Rizz071/GearTest/Docs/2016_10_17_13_23_45.png

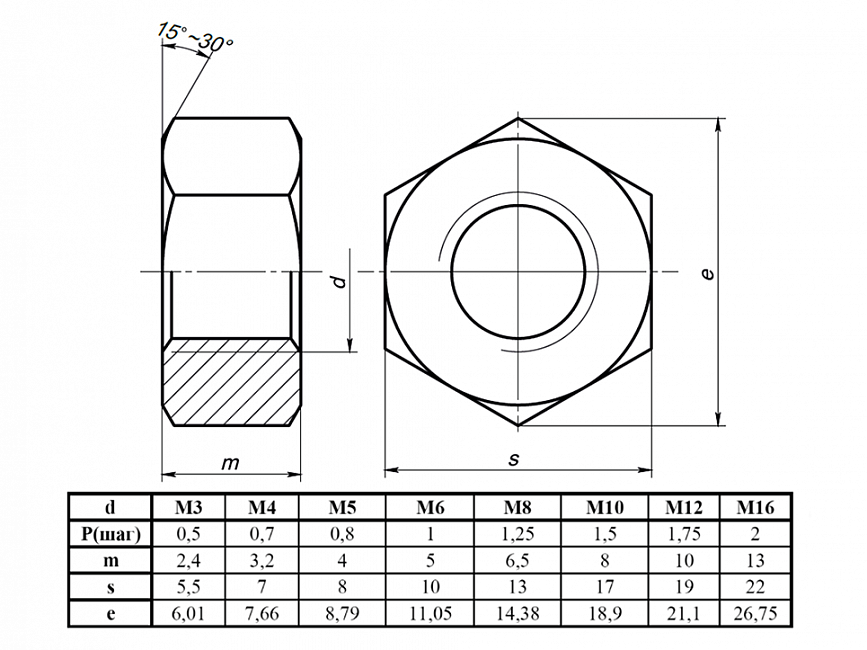
Docs/2016_10_17_13_23_45.png
