Rizz071/GearTest/Docs/6924317209.webp

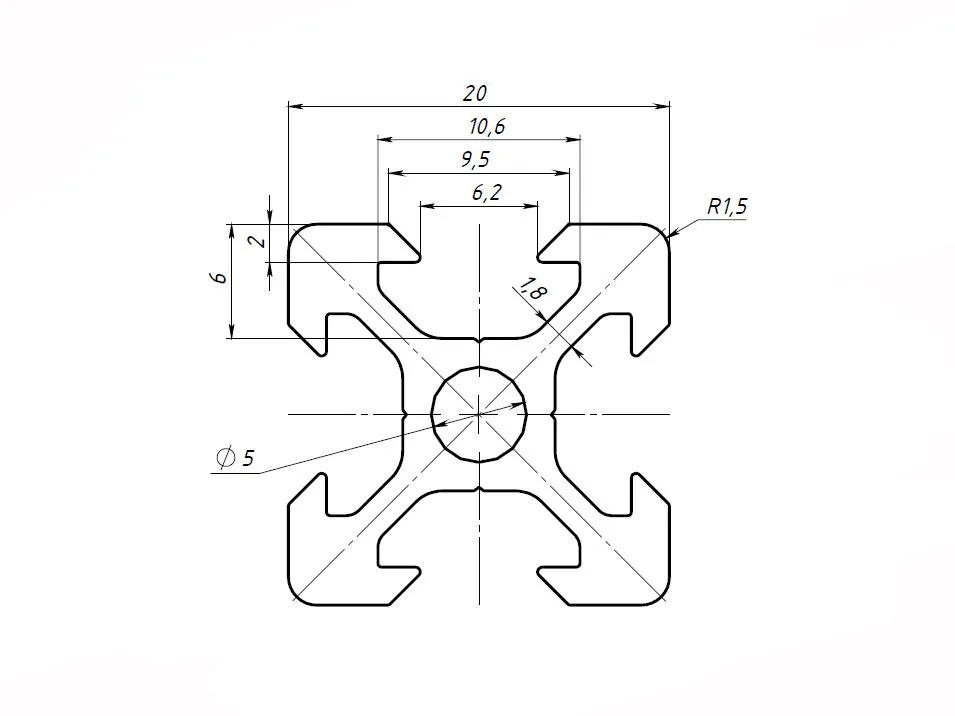
Docs/6924317209.webp
