Rizz071/GearTest/Docs/A263_CHertezh.jpg

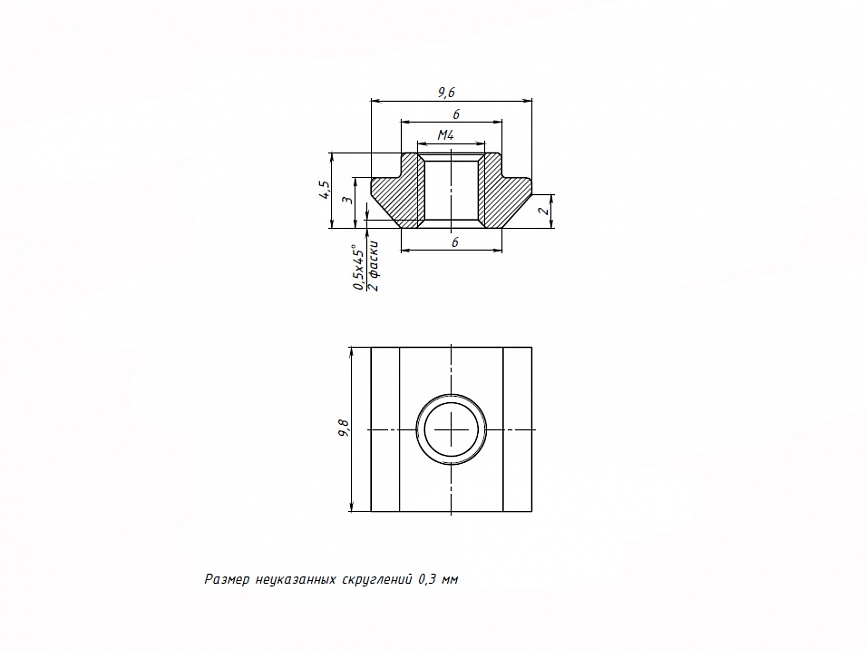
Docs/A263_CHertezh.jpg
