Rizz071/GearTest/Docs/D1925 Shaft Copuling.webp

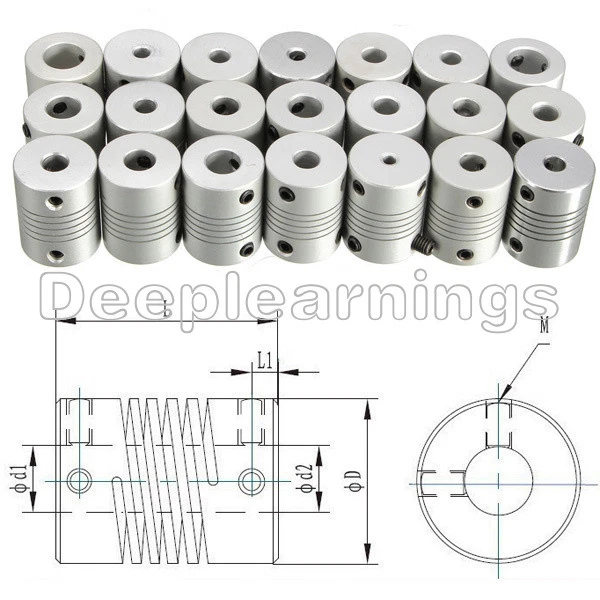
Docs/D1925 Shaft Copuling.webp
