Rizz071/GearTest/Docs/DC099 power connector.webp

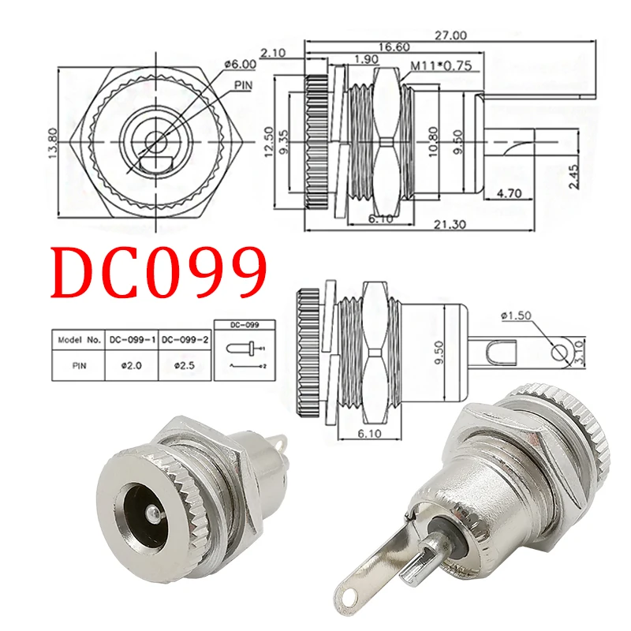
Docs/DC099 power connector.webp
