Rizz071/GearTest/Docs/DIN_912.png

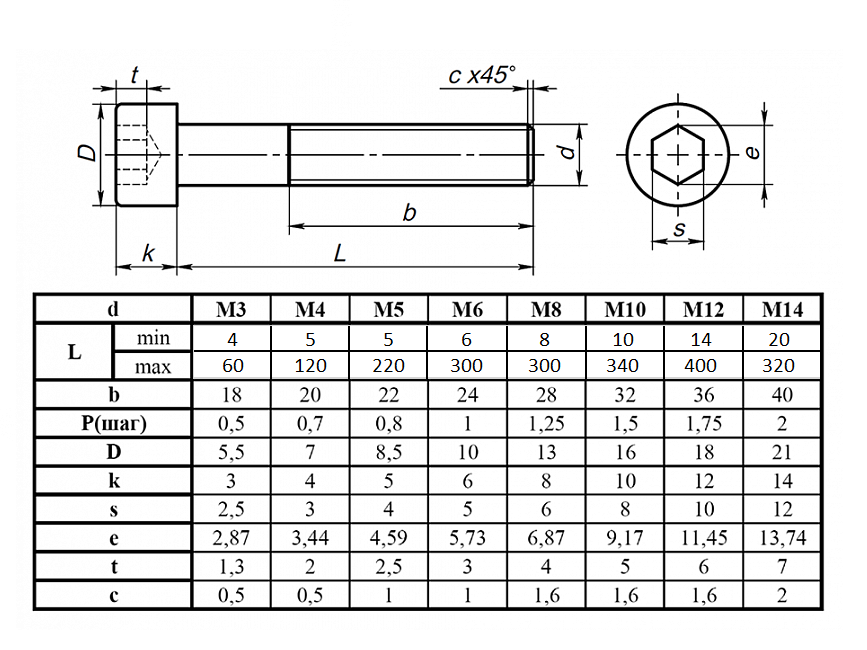
Docs/DIN_912.png
