Rizz071/GearTest/Docs/S8874a2761c8b45d180c093dec0598189X.webp

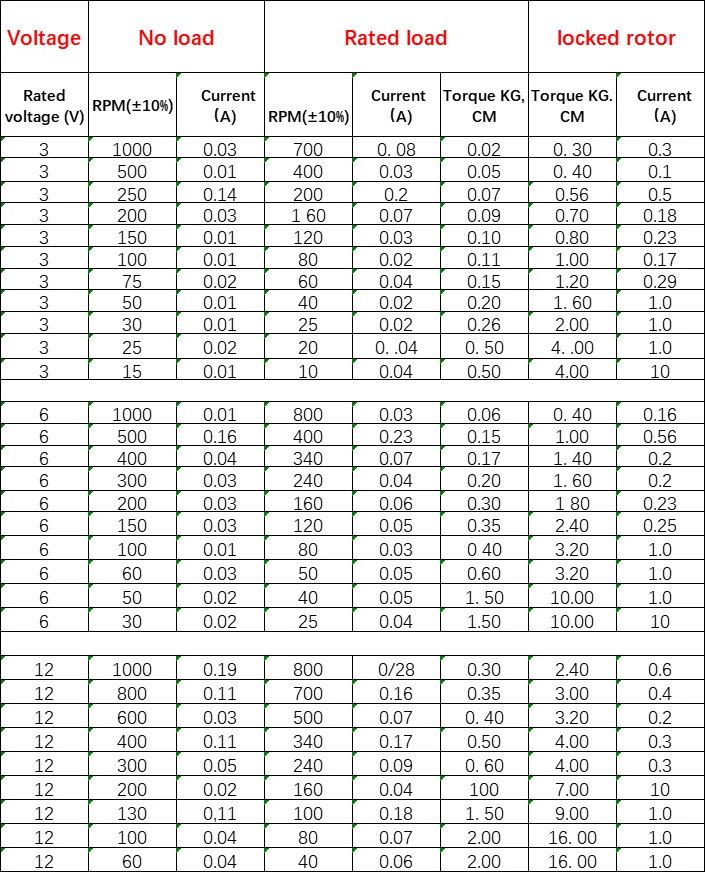
Docs/S8874a2761c8b45d180c093dec0598189X.webp
