Rizz071/GearTest/Docs/s-l500.jpg

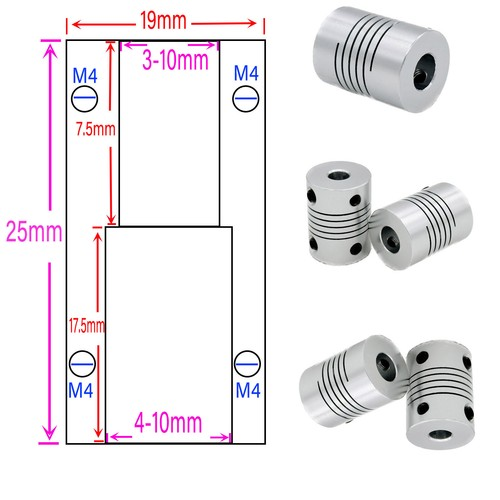
Docs/s-l500.jpg
