Rizz071/GearTest/Docs/Saec4fb16f0ac4052b8deea24fd4c7600e.webp

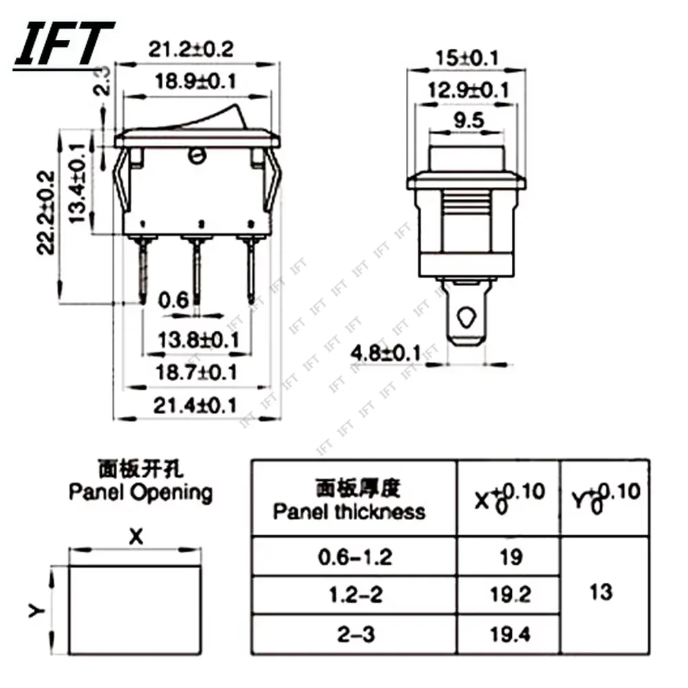
Docs/Saec4fb16f0ac4052b8deea24fd4c7600e.webp
