Rizz071/GearTest/Docs/Untitled.png

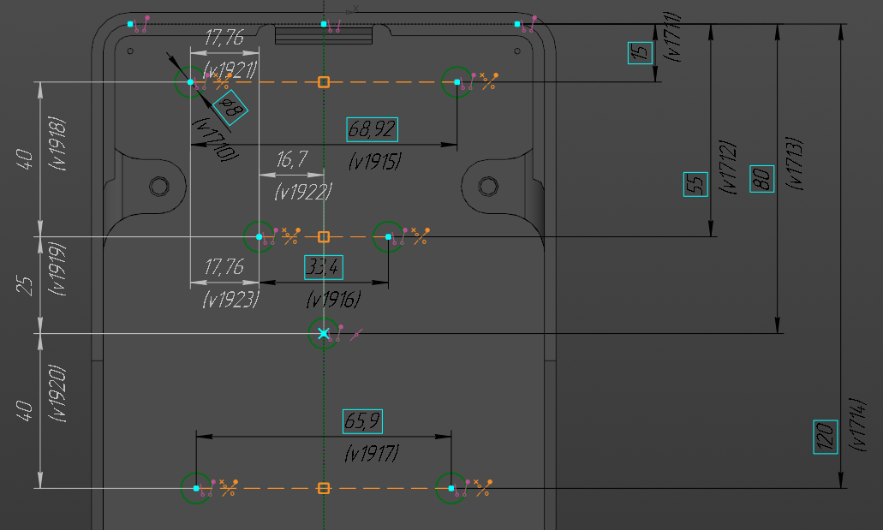
Docs/Untitled.png
