Rizz071/GearTest/CAD/KF128-2.54-8P.step

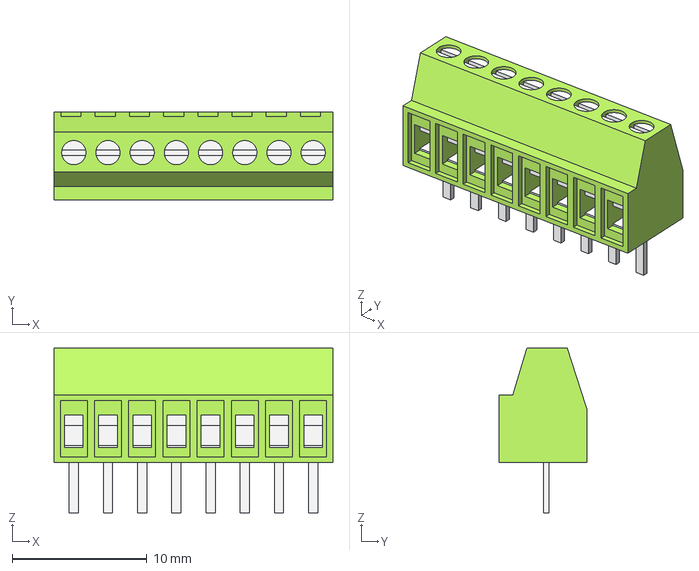
[picture p34: CAD file, 2026-03-17]
CAD/KF128-2.54-8P.step
20.7 x 6.50 x 12.3 mm
Housing
PlasticBody
