Rizz071/GearTest/CAD/KF128-2.54-11P.step

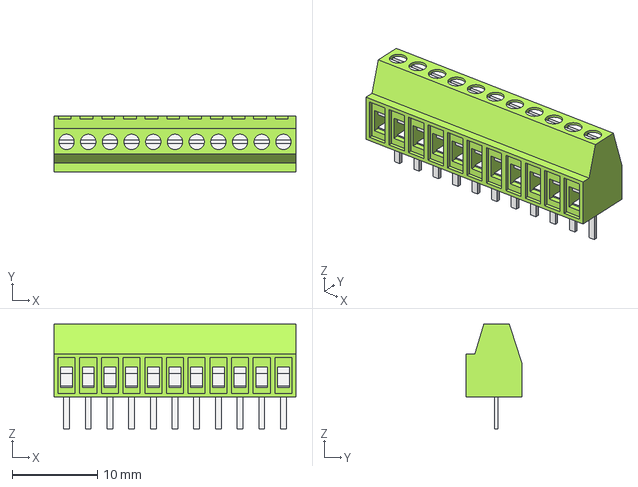
[picture p35: CAD file, 2026-03-17]
CAD/KF128-2.54-11P.step
28.3 x 6.50 x 12.3 mm
Housing
PlasticBody
