Rizz071/GearTest/CAD/KF128-2.54-10P.step

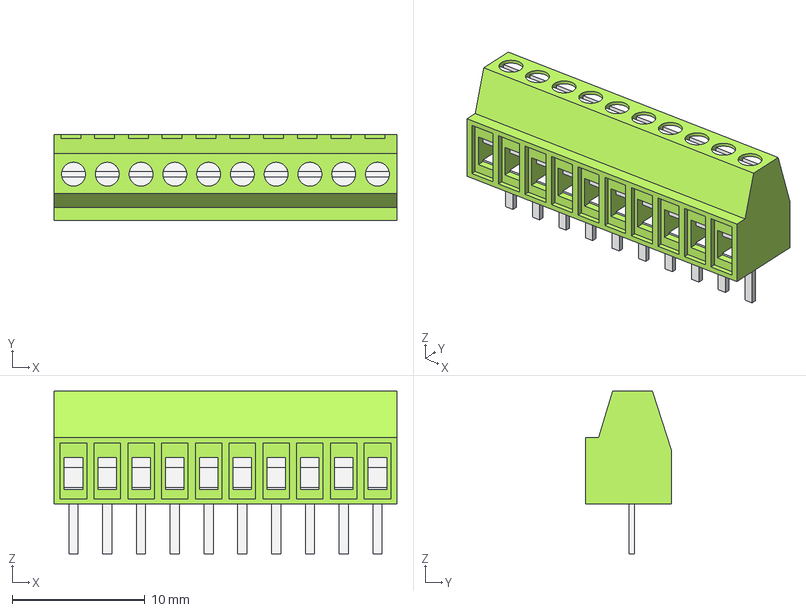
[picture p36: CAD file, 2026-03-17]
CAD/KF128-2.54-10P.step
25.8 x 6.50 x 12.3 mm
Housing
PlasticBody
