Rizz071/GearTest/CAD/KF128-2.54-12P.step

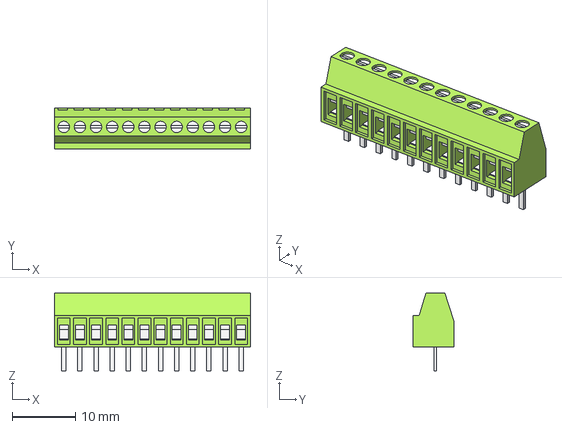
[picture p37: CAD file, 2026-03-17]
CAD/KF128-2.54-12P.step
30.9 x 6.50 x 12.3 mm
Housing
PlasticBody
