Rizz071/GearTest/CAD/KF128-2.54-2P.step

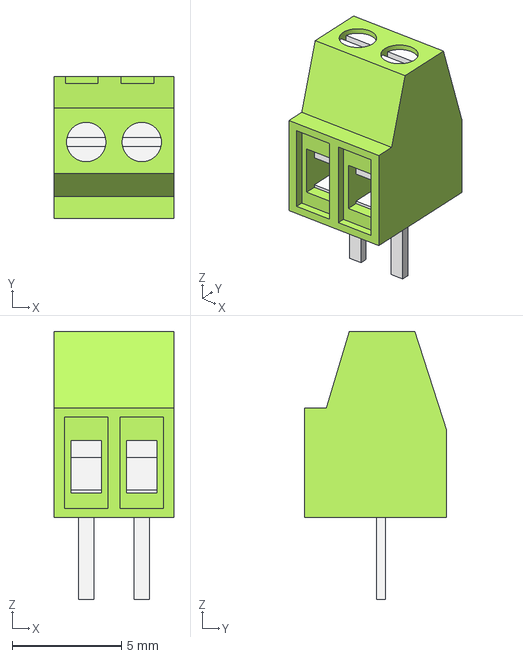
[picture p38: CAD file, 2026-03-17]
CAD/KF128-2.54-2P.step
5.48 x 6.50 x 12.3 mm
Housing
PlasticBody
