Rizz071/GearTest/CAD/KF128-2.54-7P.step

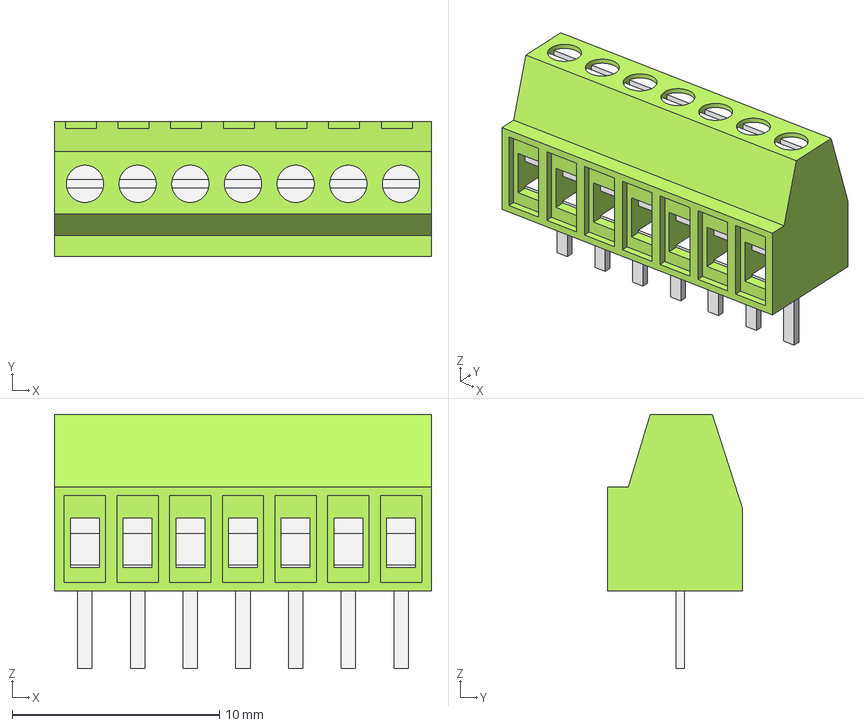
[picture p39: CAD file, 2026-03-17]
CAD/KF128-2.54-7P.step
18.2 x 6.50 x 12.3 mm
Housing
PlasticBody
