Rizz071/GearTest/CAD/LCD1602--3DModel-STEP-510211.STEP

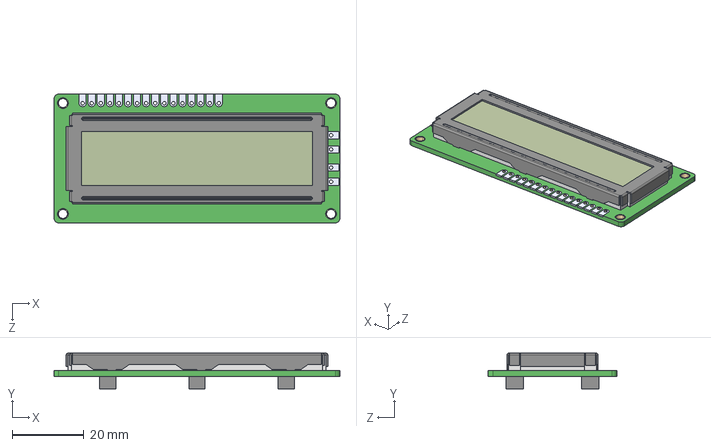
[picture p40: CAD file, 2026-03-17]
CAD/LCD1602--3DModel-STEP-510211.STEP
80.0 x 10.0 x 36.0 mm
