Rizz071/GearTest/CAD/microSD_module_band_pins.step

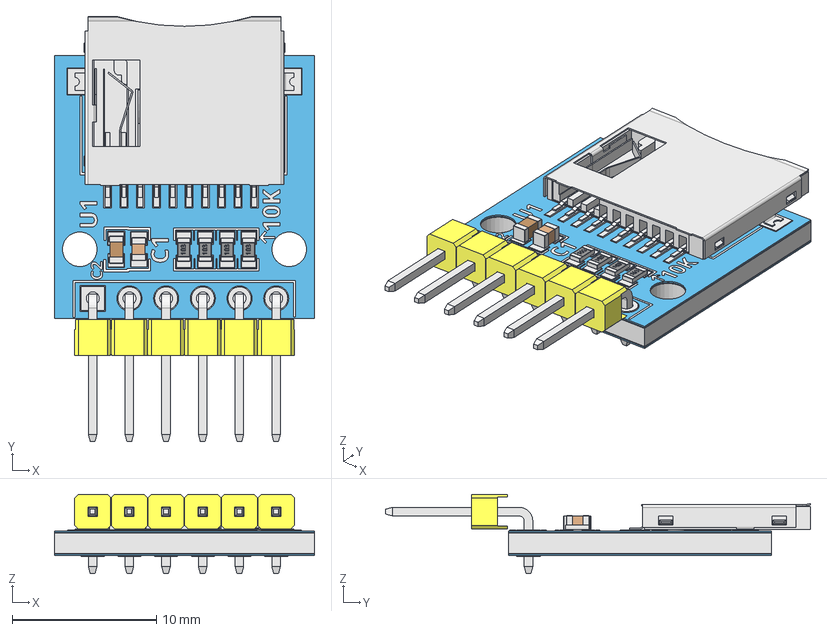
[picture p41: CAD file, 2026-03-17]
CAD/microSD_module_band_pins.step
18.0 x 29.4 x 5.50 mm
board_body
mask_up
mask_bt
metal_bt
metal_up
silk001
silk002
silk003
silk004
silk005
silk007
silk008
10K
U1
C1
C2
3V3
CS
MOSI
CLK001
MISO
GND001
sd_cover
conn001
conn002
conn003
conn004
conn005
conn006
conn007
conn008
conn009
conn010
pin011
label006
ShapeString009
pin012
pin013
label007
ShapeString010
pin014
pin015
label008
ShapeString011
pin016
pin017
label009
ShapeString012
pin018
contact019
contact020
contact033
contact034
Pin005
Pin006
Pin007
Pin008
Pin009
Pin010
Frame001
