Rizz071/GearTest/CAD/microSD_breakout_mini.step

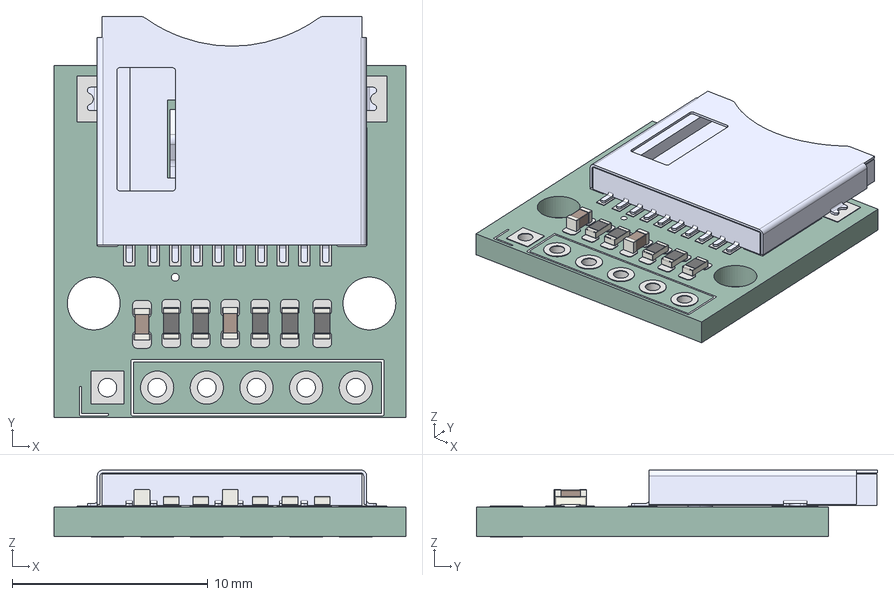
[picture p42: CAD file, 2026-03-15]
CAD/microSD_breakout_mini.step
18.0 x 20.5 x 3.47 mm
R_0603_1608Metric x 5
C_0603_1608Metric x 2
MSD-11-A
microSD_breakout_mini_pad
microSD_breakout_mini_silkscreen x 2
microSD_breakout_mini_PCB
