Rizz071/GearTest/Docs/KCD1_Wiring.jpg

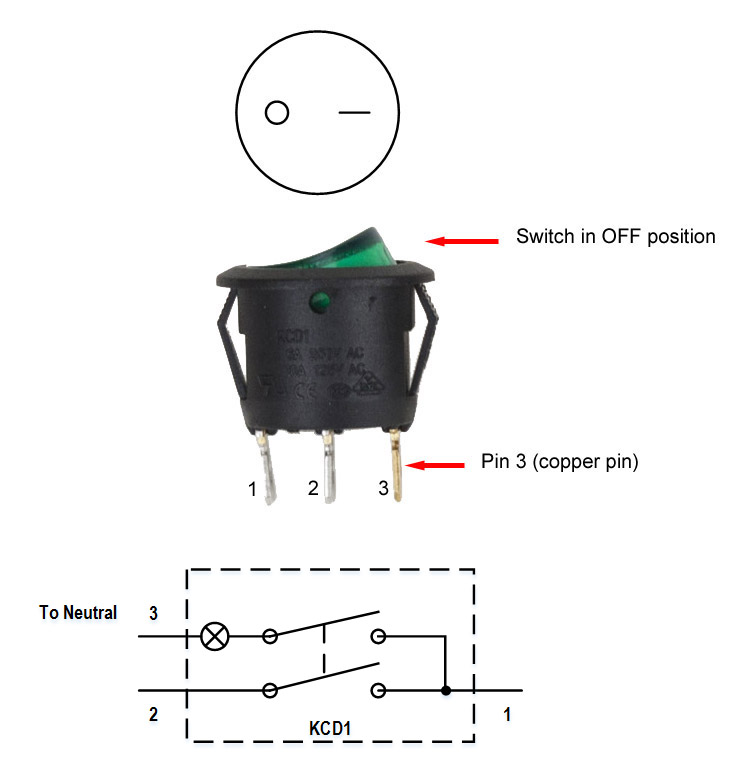
Docs/KCD1_Wiring.jpg
